Gieneq/FFTBlock/Components/Generator/dac_sines.c

#include "dac_sines.h"
#include <math.h>

const uint16_t dac_samples_values[DAC_SAMPLES_VALUES_COUNT] = {
 2048,  2245,  2441,  2632,  2818,  2996,  3166,  3324, 
 3471,  3603,  3721,  3822,  3907,  3973,  4021,  4050, 
 4060,  4050,  4021,  3973,  3907,  3822,  3721,  3603, 
 3471,  3324,  3166,  2996,  2818,  2632,  2441,  2245, 
 2048,  1851,  1655,  1464,  1278,  1100,   930,   772, 
  625,   493,   375,   274,   189,   123,    75,    46, 
   36,    46,    75,   123,   189,   274,   375,   493, 
  625,   772,   930,  1100,  1278,  1464,  1655,  1851, 
 2048,  2147,  2245,  2343,  2441,  2537,  2632,  2726, 
 2818,  2908,  2996,  3082,  3166,  3247,  3324,  3399, 
 3471,  3539,  3603,  3664,  3721,  3774,  3822,  3867, 
 3907,  3942,  3973,  4000,  4021,  4038,  4050,  4058, 
 4060,  4058,  4050,  4038,  4021,  4000,  3973,  3942, 
 3907,  3867,  3822,  3774,  3721,  3664,  3603,  3539, 
 3471,  3399,  3324,  3247,  3166,  3082,  2996,  2908, 
 2818,  2726,  2632,  2537,  2441,  2343,  2245,  2147, 
 2048,  1949,  1851,  1753,  1655,  1559,  1464,  1370, 
 1278,  1188,  1100,  1014,   930,   849,   772,   697, 
  625,   557,   493,   432,   375,   322,   274,   229, 
  189,   154,   123,    96,    75,    58,    46,    38, 
   36,    38,    46,    58,    75,    96,   123,   154, 
  189,   229,   274,   322,   375,   432,   493,   557, 
  625,   697,   772,   849,   930,  1014,  1100,  1188, 
 1278,  1370,  1464,  1559,  1655,  1753,  1851,  1949, 
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
	{    64, dac_samples_values +     64,    128,    101,   4950.495F },
	{   192, dac_samples_values +    192,    256,     47,   5319.149F },
	{   960, dac_samples_values +    960,   1024,     11,   5681.818F },
	{   192, dac_samples_values +    192,    256,     41,   6097.561F },
	{     0, dac_samples_values +      0,     64,    153,   6535.948F },
	{    64, dac_samples_values +     64,    128,     71,   7042.254F },
	{     0, dac_samples_values +      0,     64,    133,   7518.797F },
	{   192, dac_samples_values +    192,    256,     31,   8064.516F },
	{     0, dac_samples_values +      0,     64,    116,    8620.69F },
	{   192, dac_samples_values +    192,    256,     27,   9259.259F },
	{     0, dac_samples_values +      0,     64,    100,    10000.0F },
	{    64, dac_samples_values +     64,    128,     47,  10638.298F },
	{     0, dac_samples_values +      0,     64,     87,  11494.253F },
	{     0, dac_samples_values +      0,     64,     81,  12345.679F },
	{   192, dac_samples_values +    192,    256,     19,  13157.895F },
	{     0, dac_samples_values +      0,     64,     71,  14084.507F },
	{    64, dac_samples_values +     64,    128,     33,  15151.515F },
	{     0, dac_samples_values +      0,     64,     62,  16129.032F },
	{     0, dac_samples_values +      0,     64,     57,   17543.86F },
	{     0, dac_samples_values +      0,     64,     54,  18518.519F },
	{    64, dac_samples_values +     64,    128,     25,    20000.0F },
};
